Bastardkb/Skeletyl/pics/1.png

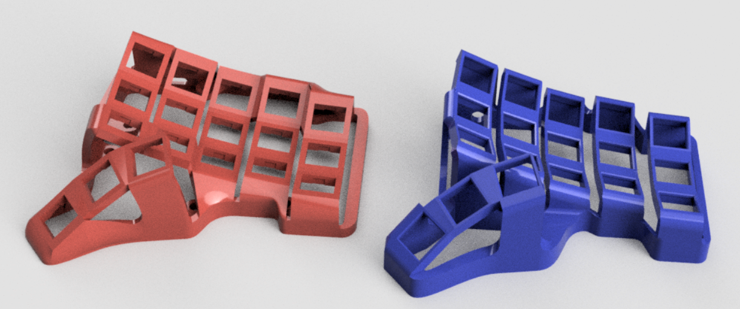
pics/1.png
