Bastardkb/Skeletyl/pics/2.jpg

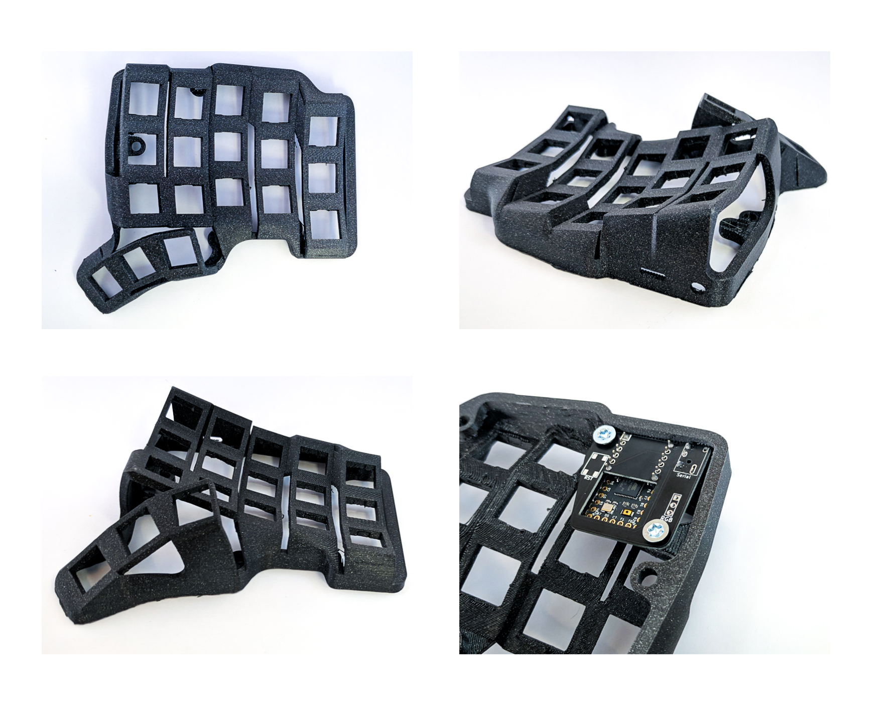
pics/2.jpg
