Bastardkb/Skeletyl/pics/2.png

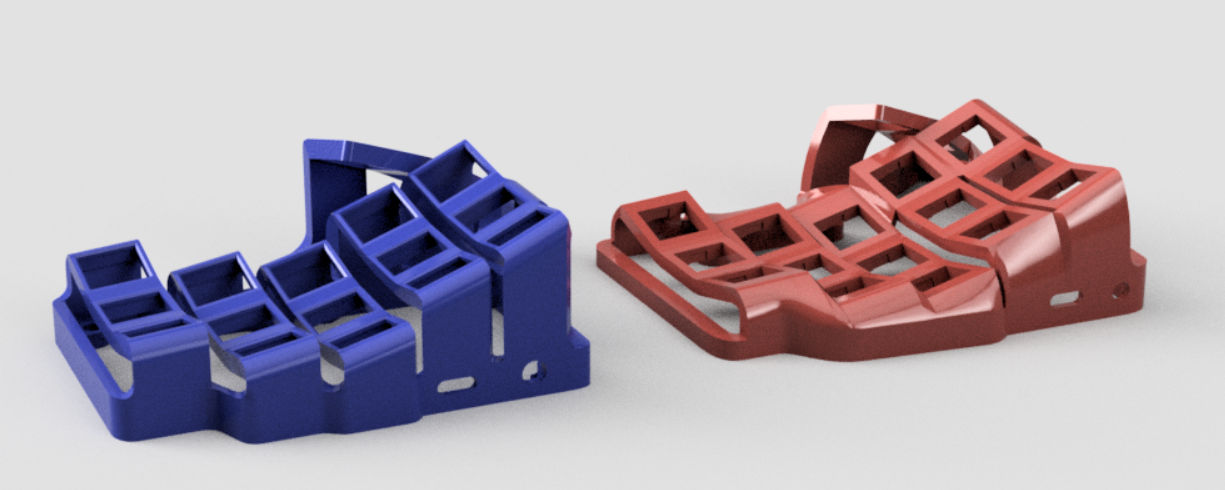
pics/2.png
