Bastardkb/Skeletyl/pics/4.jpg

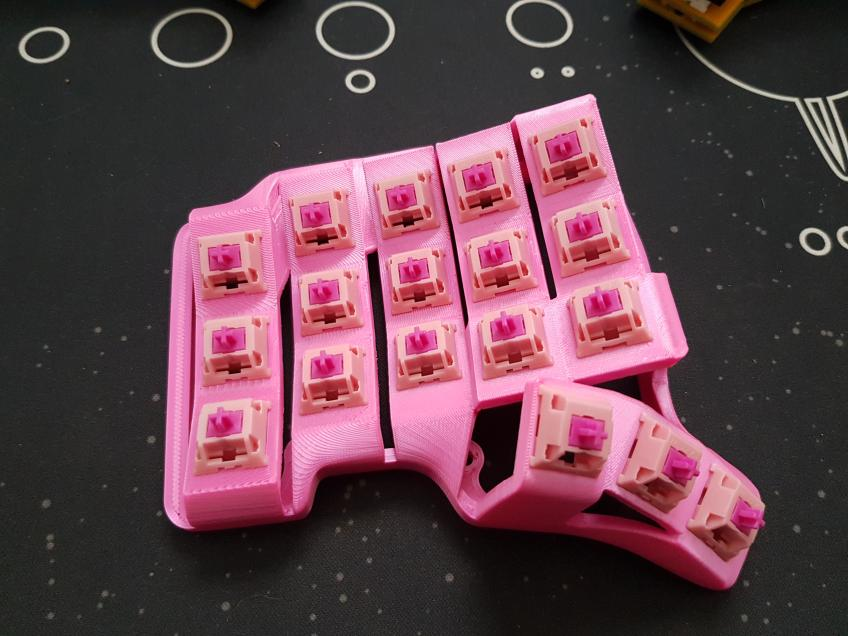
pics/4.jpg
