Bastardkb/Skeletyl/mods/magsafe/Skeletyl_v4 v105-plate-patched.stl

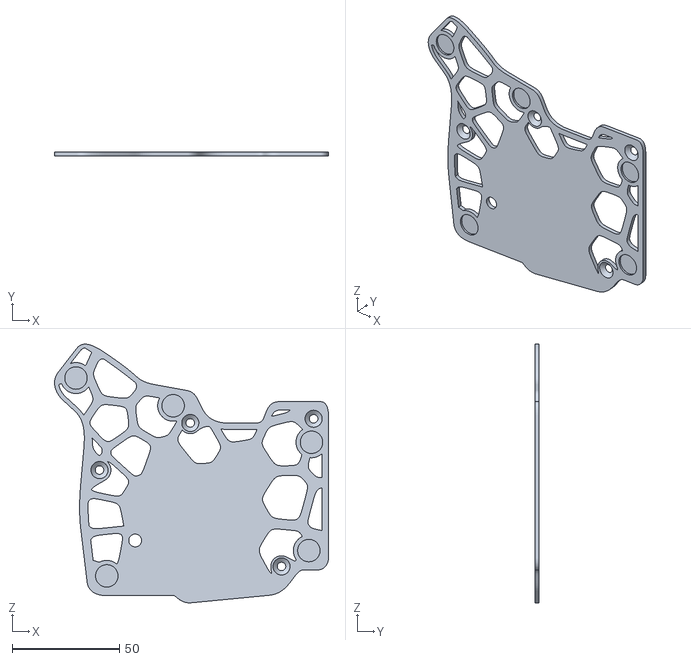
[picture p27: CAD file, 2023-06-12]
mods/magsafe/Skeletyl_v4 v105-plate-patched.stl
128.0 x 2.00 x 120.9
