Bastardkb/Skeletyl/mods/unibody/Promicro/promicro voronoi side.stl

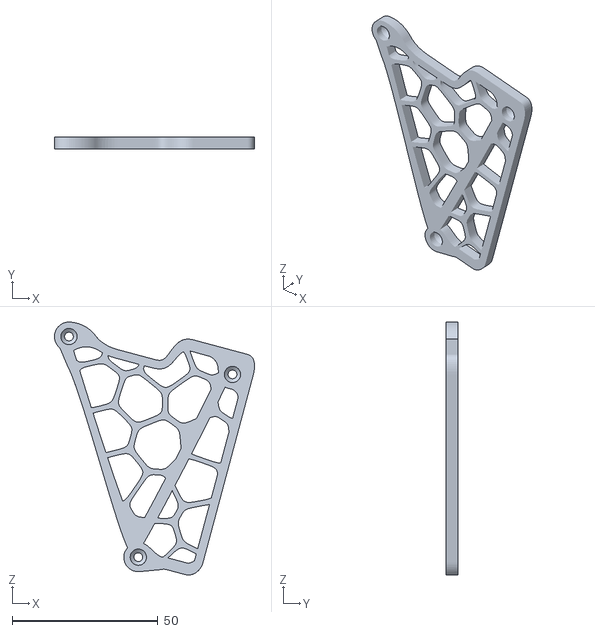
[picture p28: CAD file, 2024-03-21]
mods/unibody/Promicro/promicro voronoi side.stl
68.7 x 4.00 x 86.9
