Bastardkb/Skeletyl/V4/plates/plate_v4_103.stl

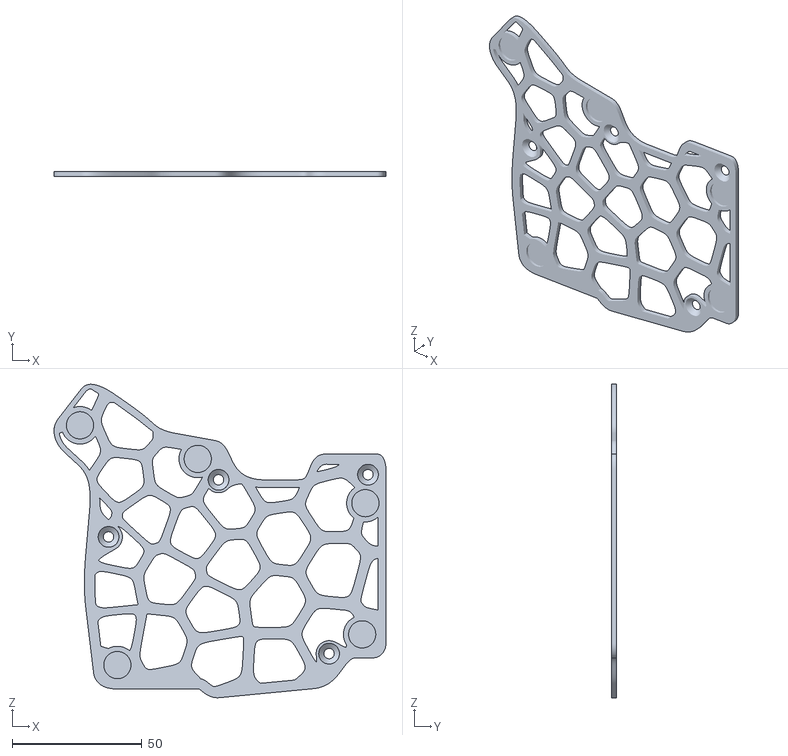
[picture p29: CAD file, 2022-06-08]
V4/plates/plate_v4_103.stl
128.0 x 2.00 x 120.9
