Bastardkb/Skeletyl/mods/magsafe/plate_magnet_v2.dxf

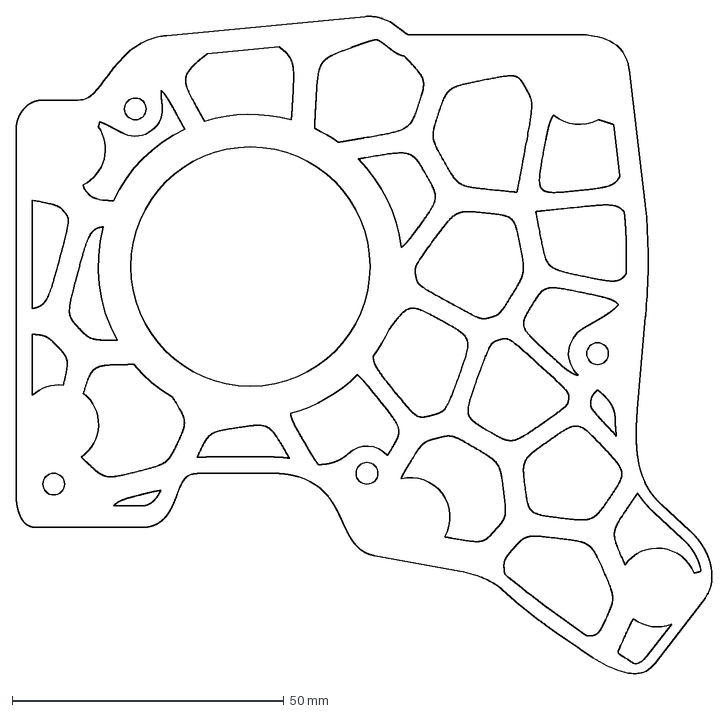
[picture p30: CAD file, 2023-03-26]
mods/magsafe/plate_magnet_v2.dxf
128.0 x 120.9 mm
